Adriana-28/Repositorio_grupo_13/Imágenes/1.png

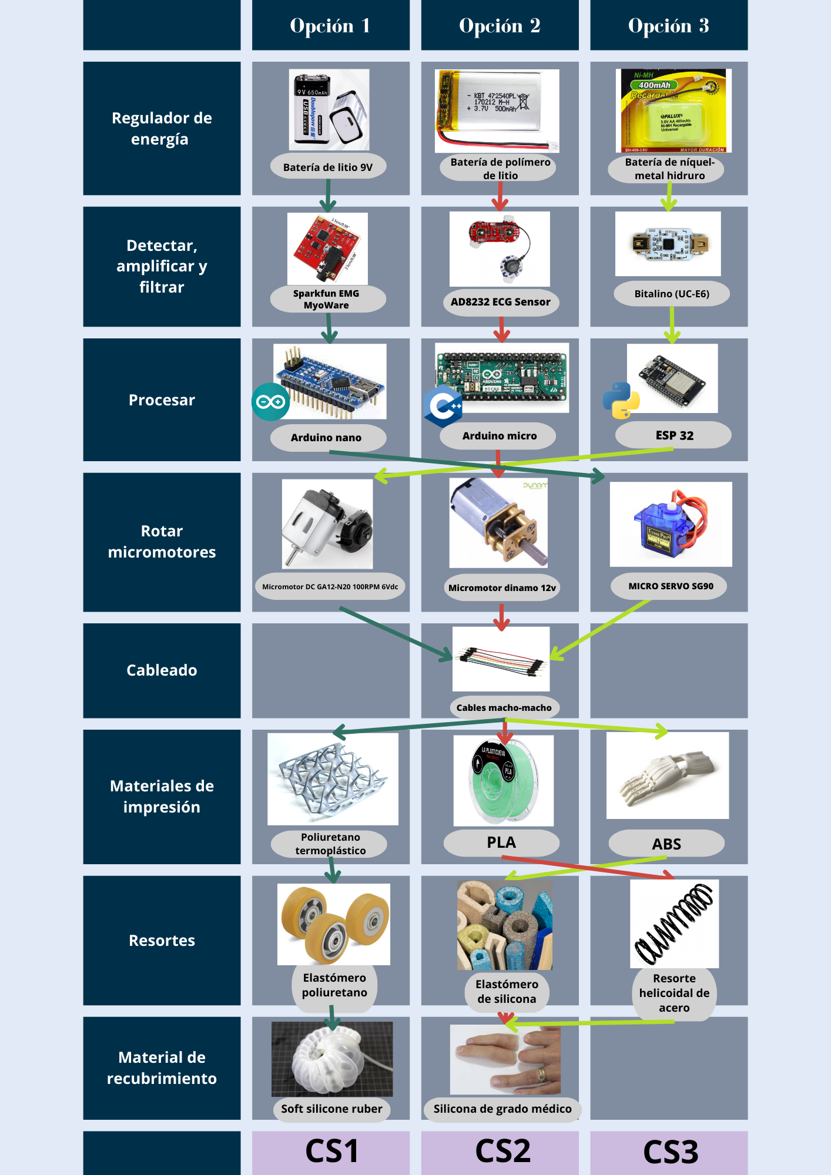
Imágenes/1.png
