Adriana-28/Repositorio_grupo_13/Imágenes/2.png

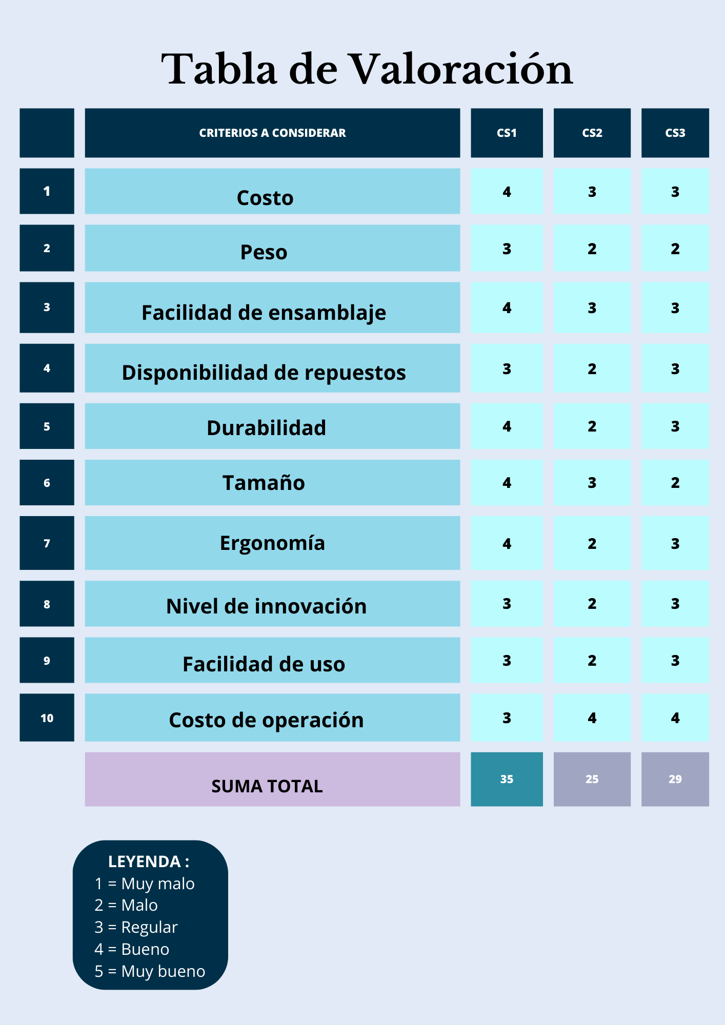
Imágenes/2.png
