Adriana-28/Repositorio_grupo_13/Imágenes/Captura de pantalla 2023-09-21 232807.png

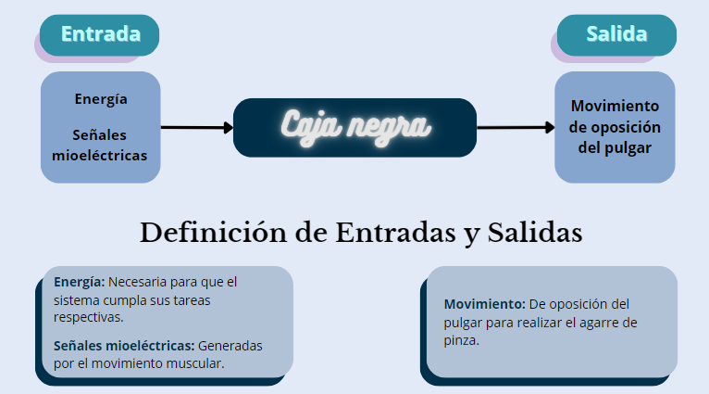
Imágenes/Captura de pantalla 2023-09-21 232807.png
