Adriana-28/Repositorio_grupo_13/Imágenes/Captura de pantalla 2023-09-21 233254.png

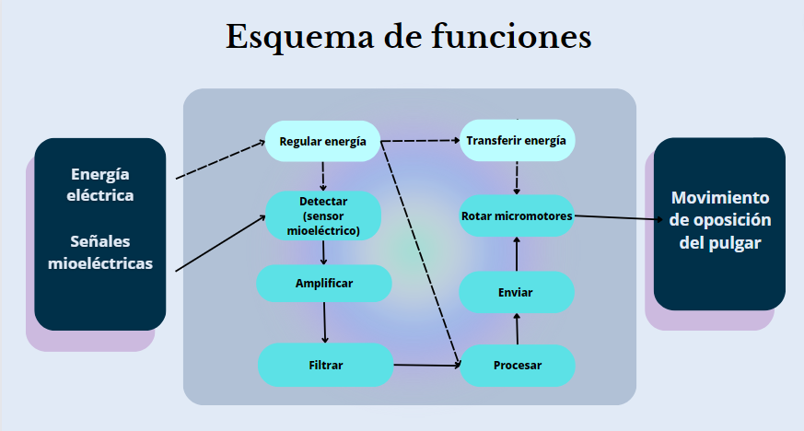
Imágenes/Captura de pantalla 2023-09-21 233254.png
