Adriana-28/Repositorio_grupo_13/Imágenes/Captura de pantalla 2023-10-20 073522.png

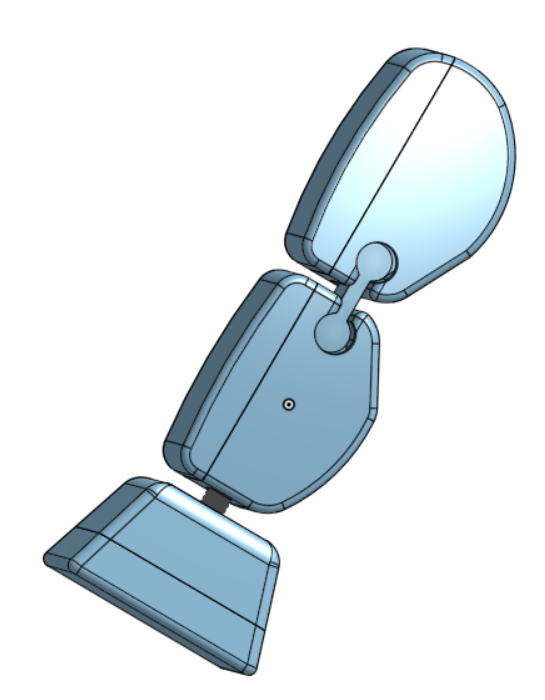
Imágenes/Captura de pantalla 2023-10-20 073522.png
