Adriana-28/Repositorio_grupo_13/Imágenes/Captura de pantalla 2023-11-03 025052.png

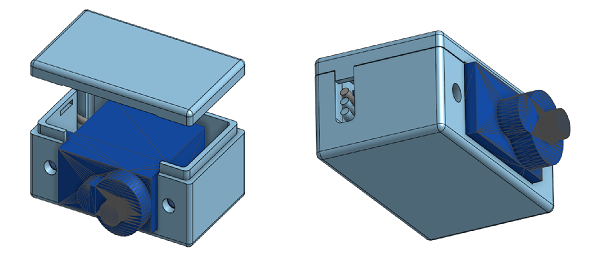
Imágenes/Captura de pantalla 2023-11-03 025052.png
