Adriana-28/Repositorio_grupo_13/Imágenes/Captura de pantalla 2023-11-24 012323.png

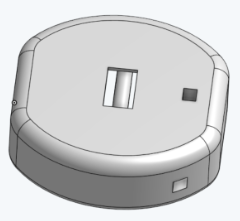
Imágenes/Captura de pantalla 2023-11-24 012323.png
