Adriana-28/Repositorio_grupo_13/Imágenes/Captura de pantalla 2023-11-24 012328.png

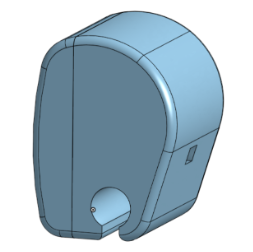
Imágenes/Captura de pantalla 2023-11-24 012328.png
