Adriana-28/Repositorio_grupo_13/Imágenes/Esquema de funciones.png

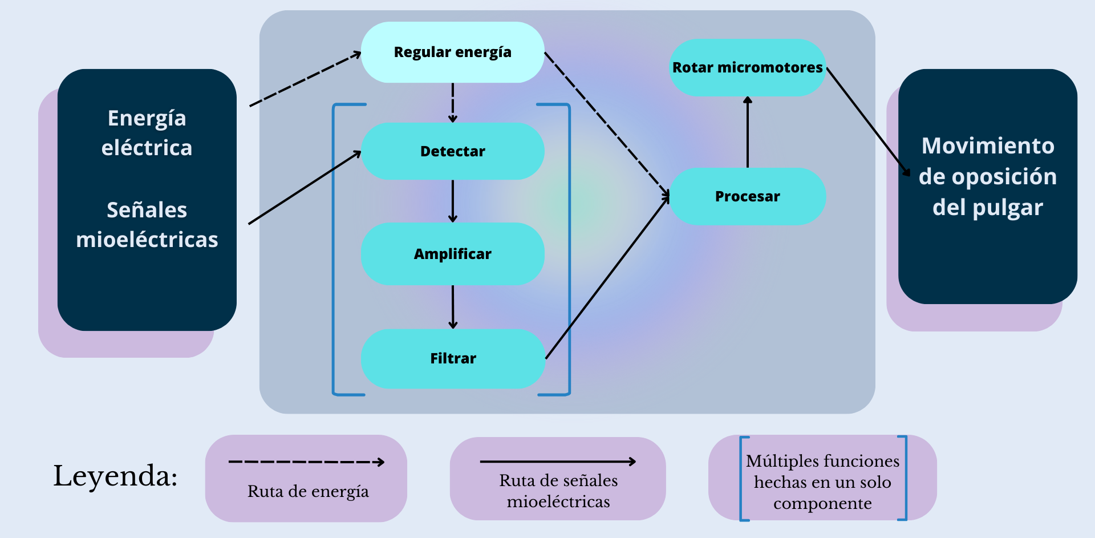
Imágenes/Esquema de funciones.png
