Adriana-28/Repositorio_grupo_13/Imágenes/Foto Alessia.jpeg

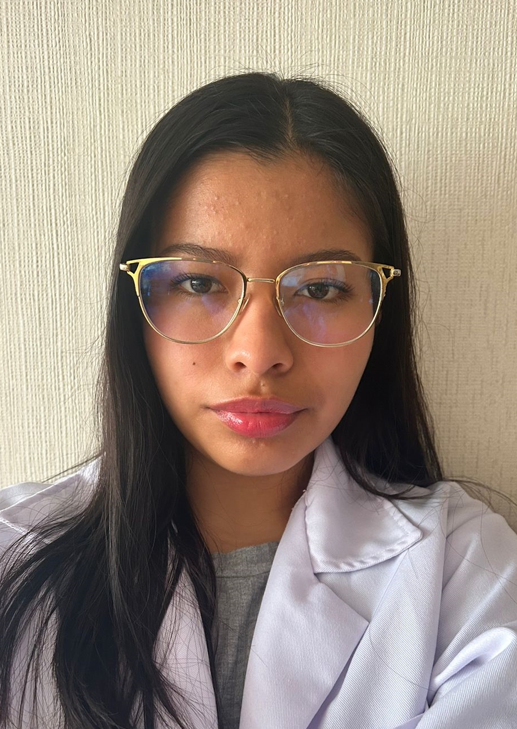
Imágenes/Foto Alessia.jpeg
