Adriana-28/Repositorio_grupo_13/Imágenes/Matriz morfológica (1).png

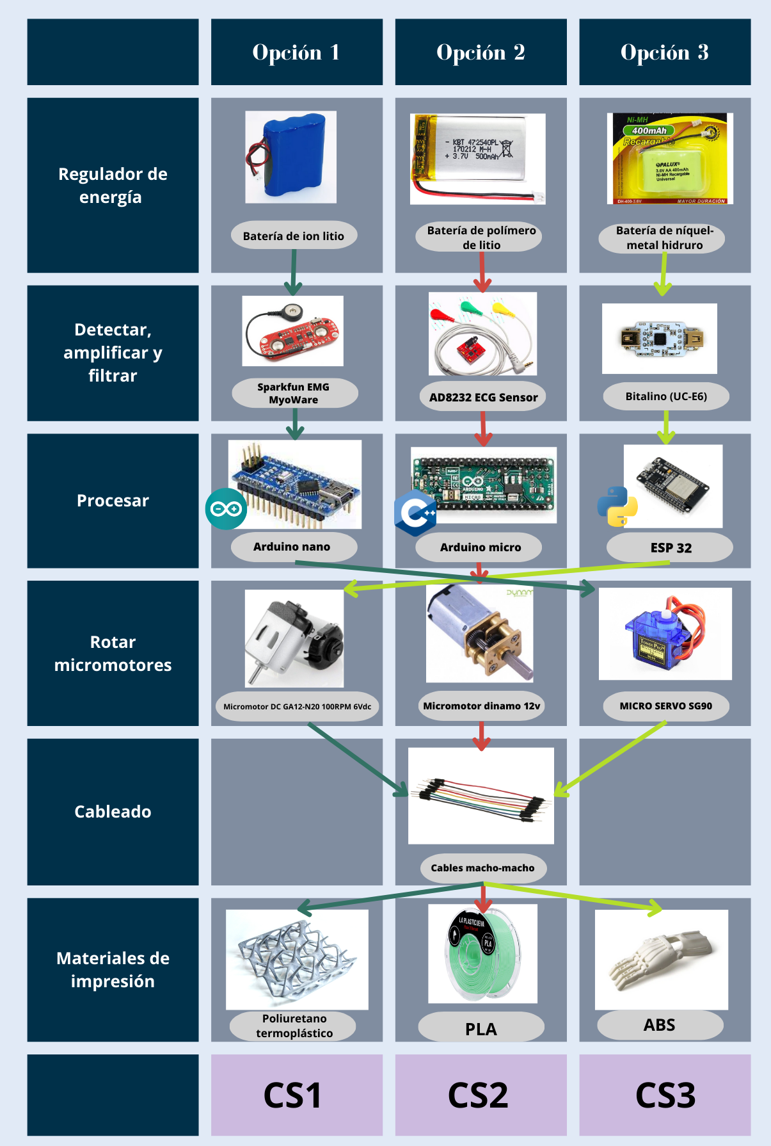
Imágenes/Matriz morfológica (1).png
