Adriana-28/Repositorio_grupo_13/Imágenes/Patente mano.jpeg

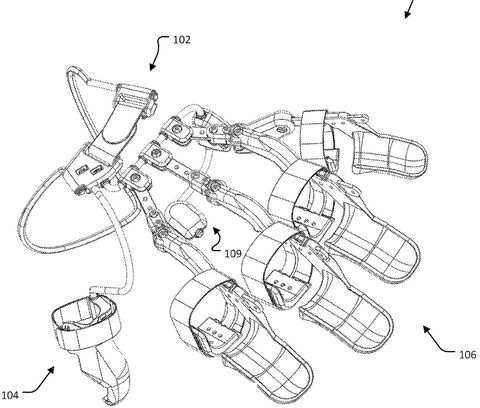
Imágenes/Patente mano.jpeg
