Adriana-28/Repositorio_grupo_13/Imágenes/Patente pulgar.jpeg

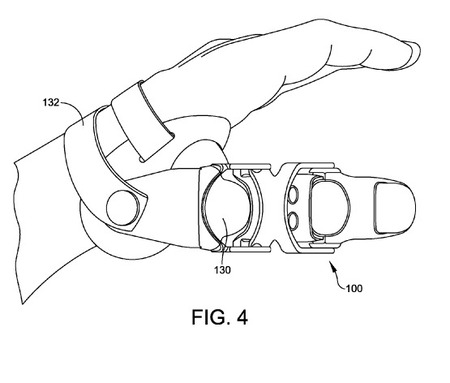
Imágenes/Patente pulgar.jpeg
