Adriana-28/Repositorio_grupo_13/Imágenes/Tabla de valoración.png

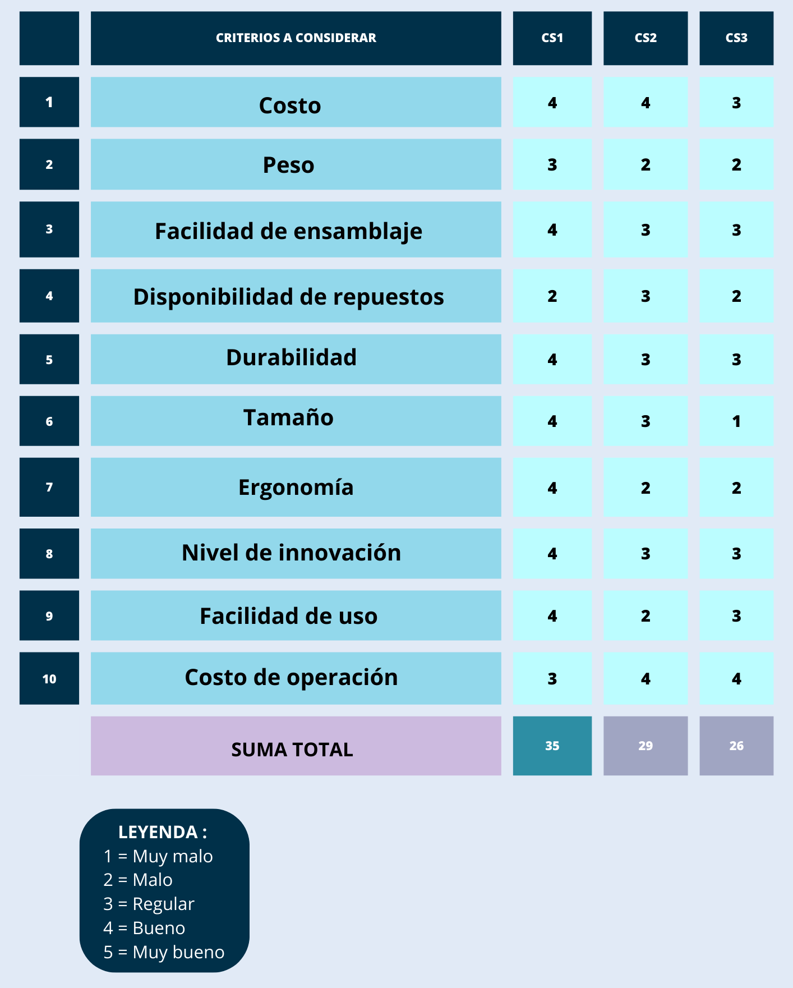
Imágenes/Tabla de valoración.png
