Adriana-28/Repositorio_grupo_13/Imágenes/WhatsApp Image 2023-09-21 at 20.53.01.jpeg

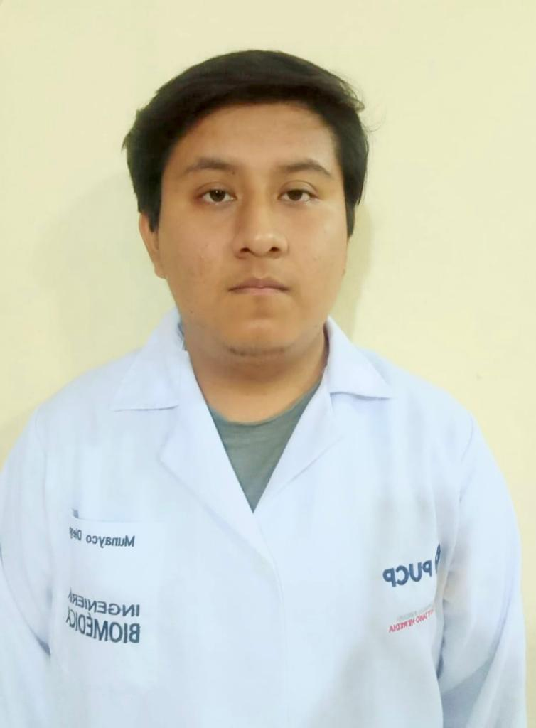
Imágenes/WhatsApp Image 2023-09-21 at 20.53.01.jpeg
