Adriana-28/Repositorio_grupo_13/Imágenes/WhatsApp Image 2023-09-21 at 22.54.08.jpeg

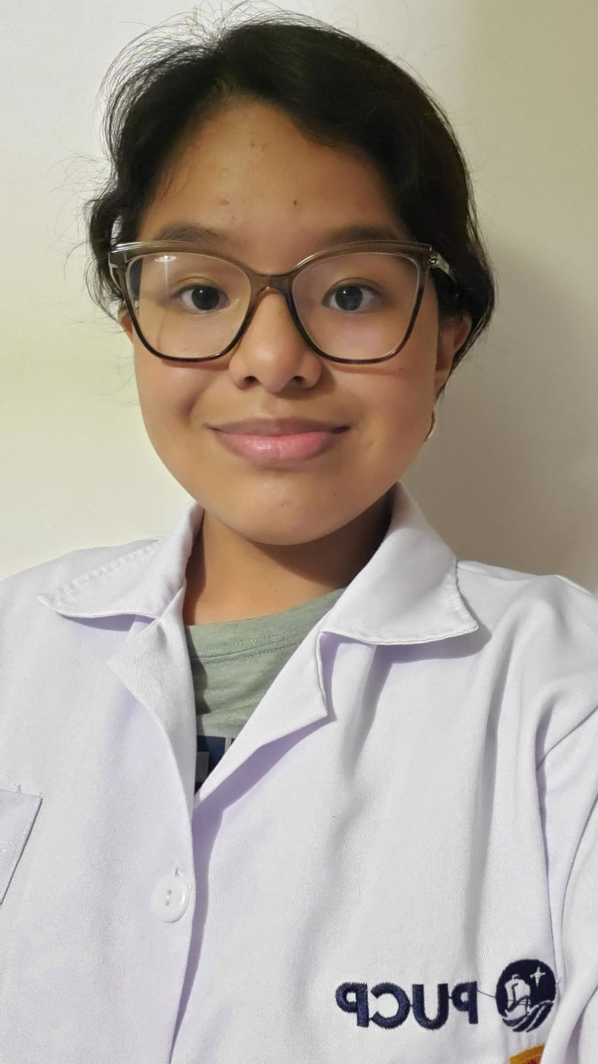
Imágenes/WhatsApp Image 2023-09-21 at 22.54.08.jpeg
