Adriana-28/Repositorio_grupo_13/Imágenes/WhatsApp Image 2023-09-28 at 23.58.50.jpeg

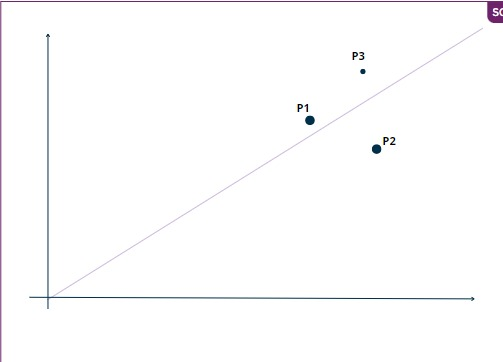
Imágenes/WhatsApp Image 2023-09-28 at 23.58.50.jpeg
