Adriana-28/Repositorio_grupo_13/Imágenes/WhatsApp Image 2023-11-03 at 02.50.23.jpeg

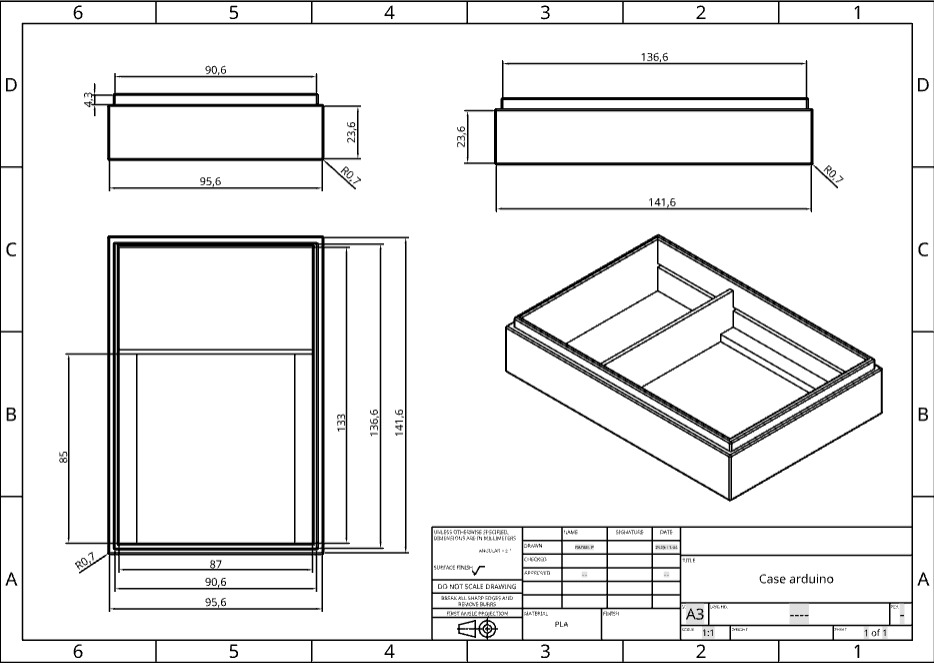
Imágenes/WhatsApp Image 2023-11-03 at 02.50.23.jpeg
