Adriana-28/Repositorio_grupo_13/Modelado/Planos de las piezas/Base_1.pdf

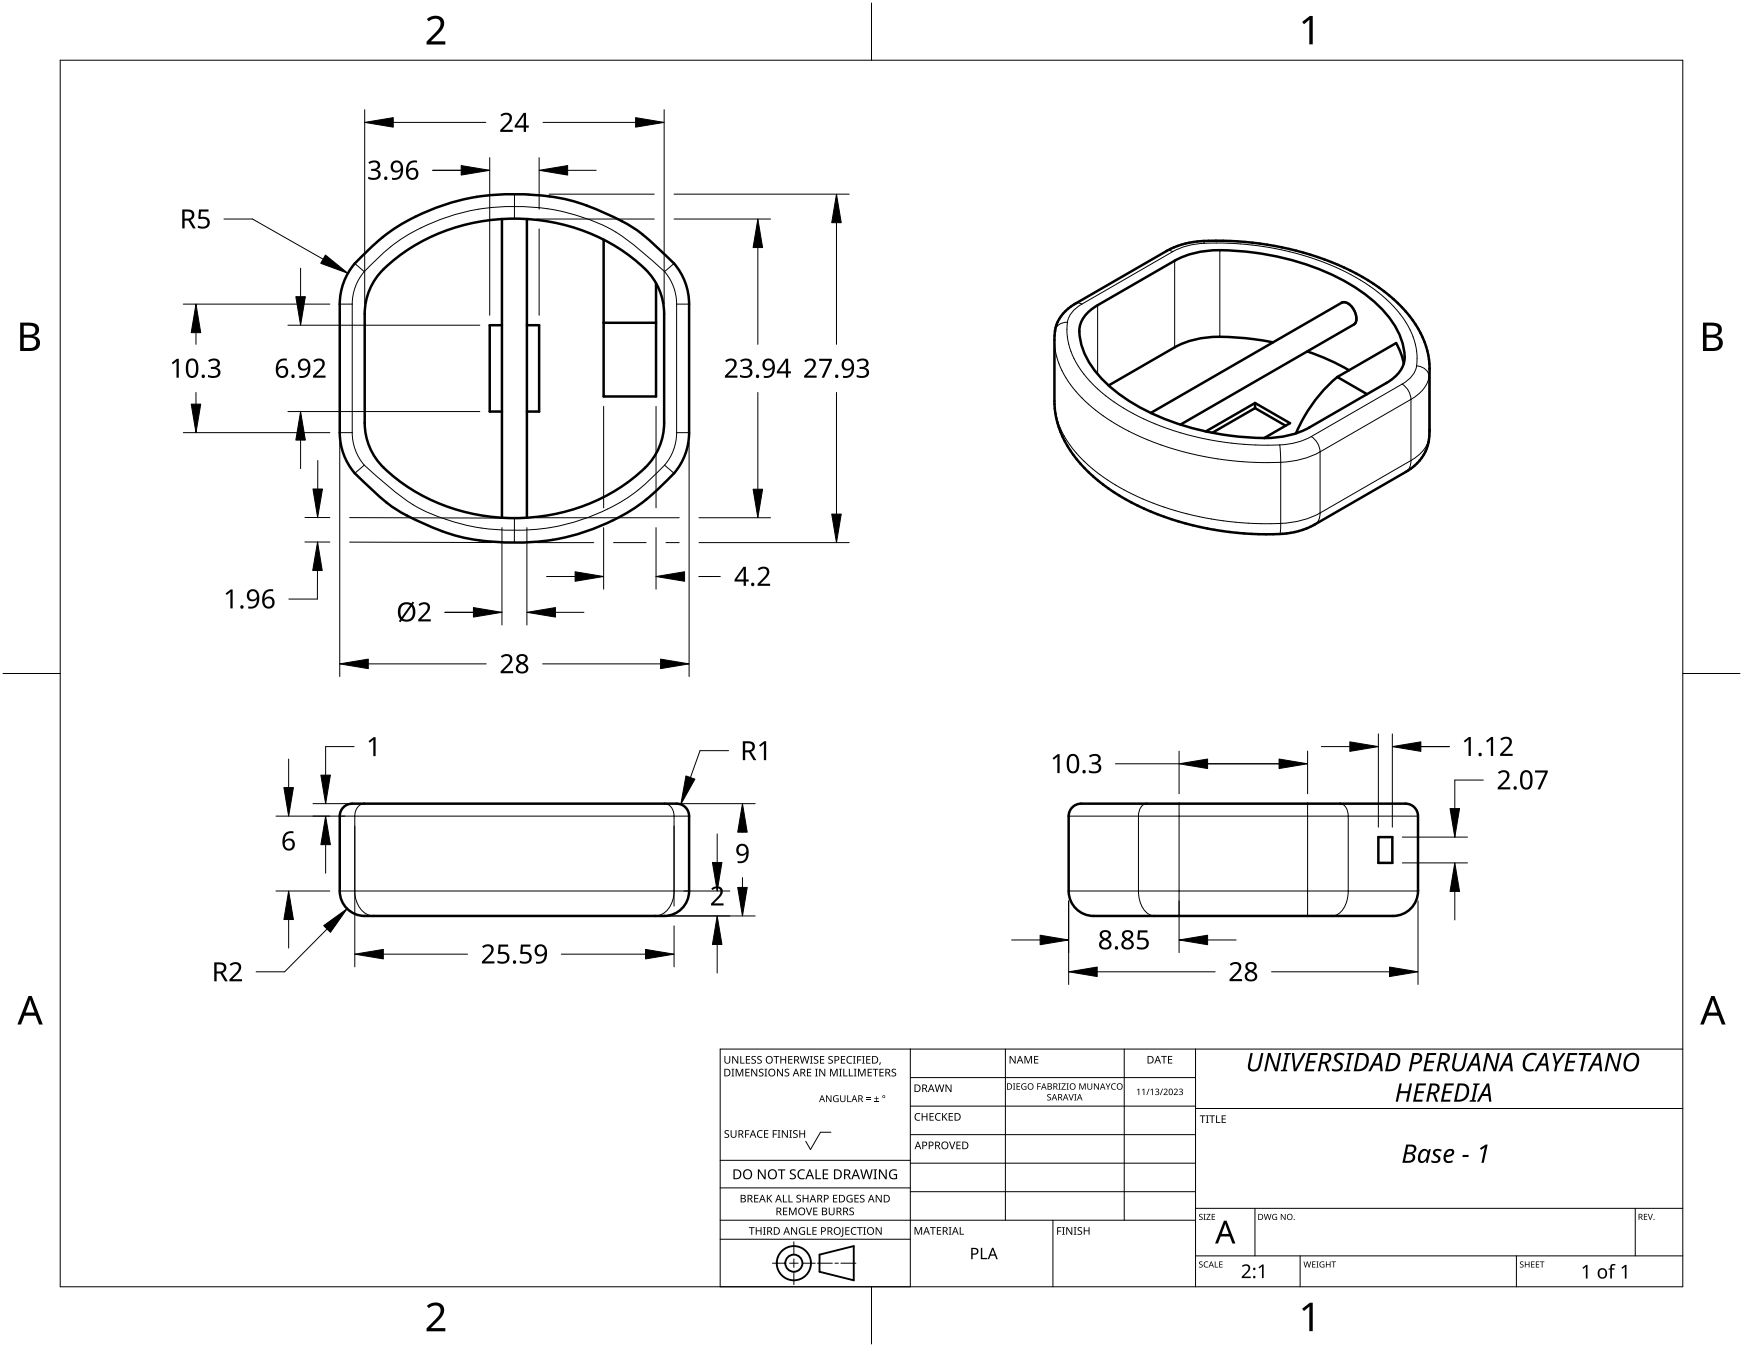
[picture p146: page 1]
