Adriana-28/Repositorio_grupo_13/Modelado/Planos de las piezas/Base_2.pdf

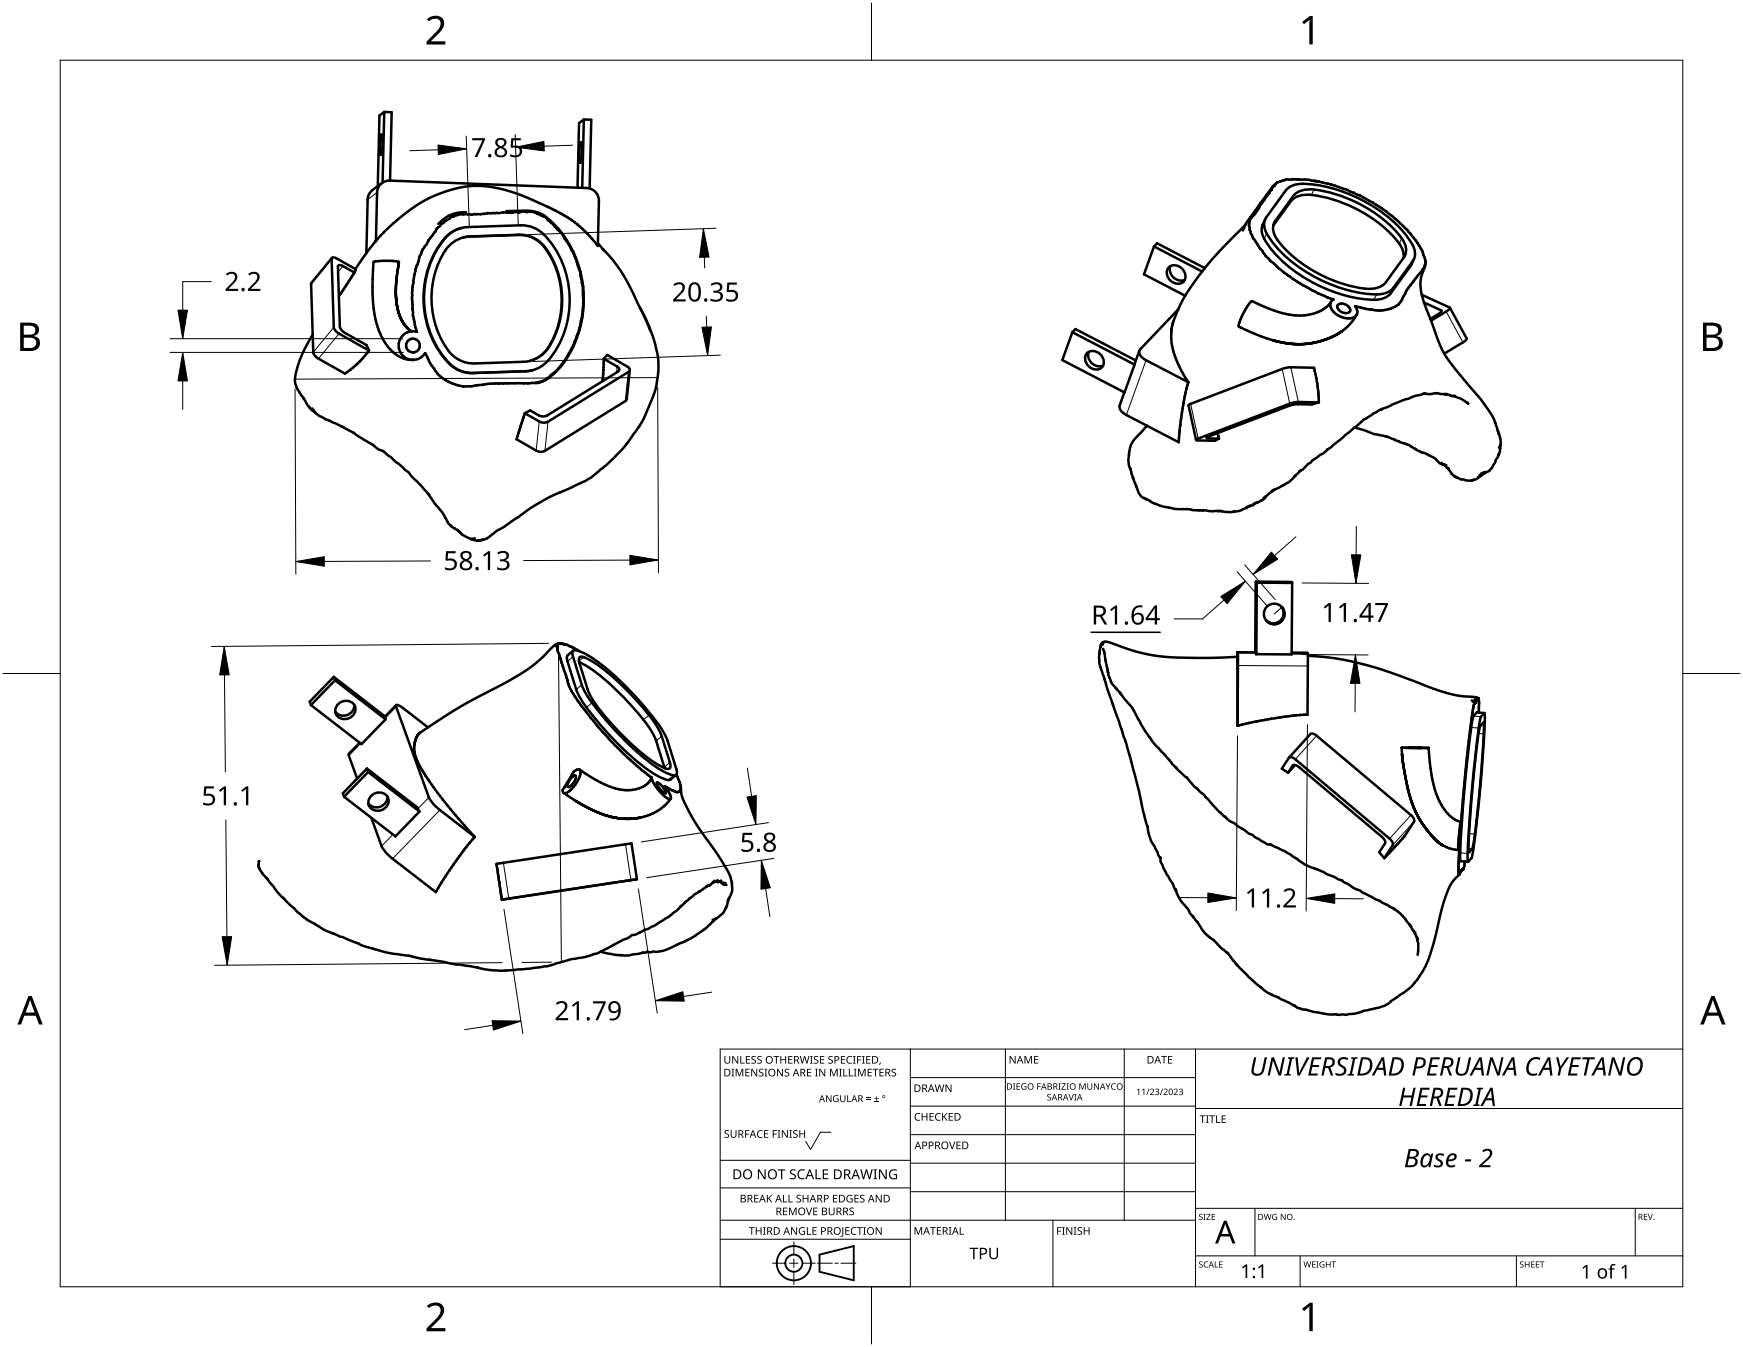
[picture p147: page 1]
