Adriana-28/Repositorio_grupo_13/Modelado/Planos de las piezas/Elastómero.pdf

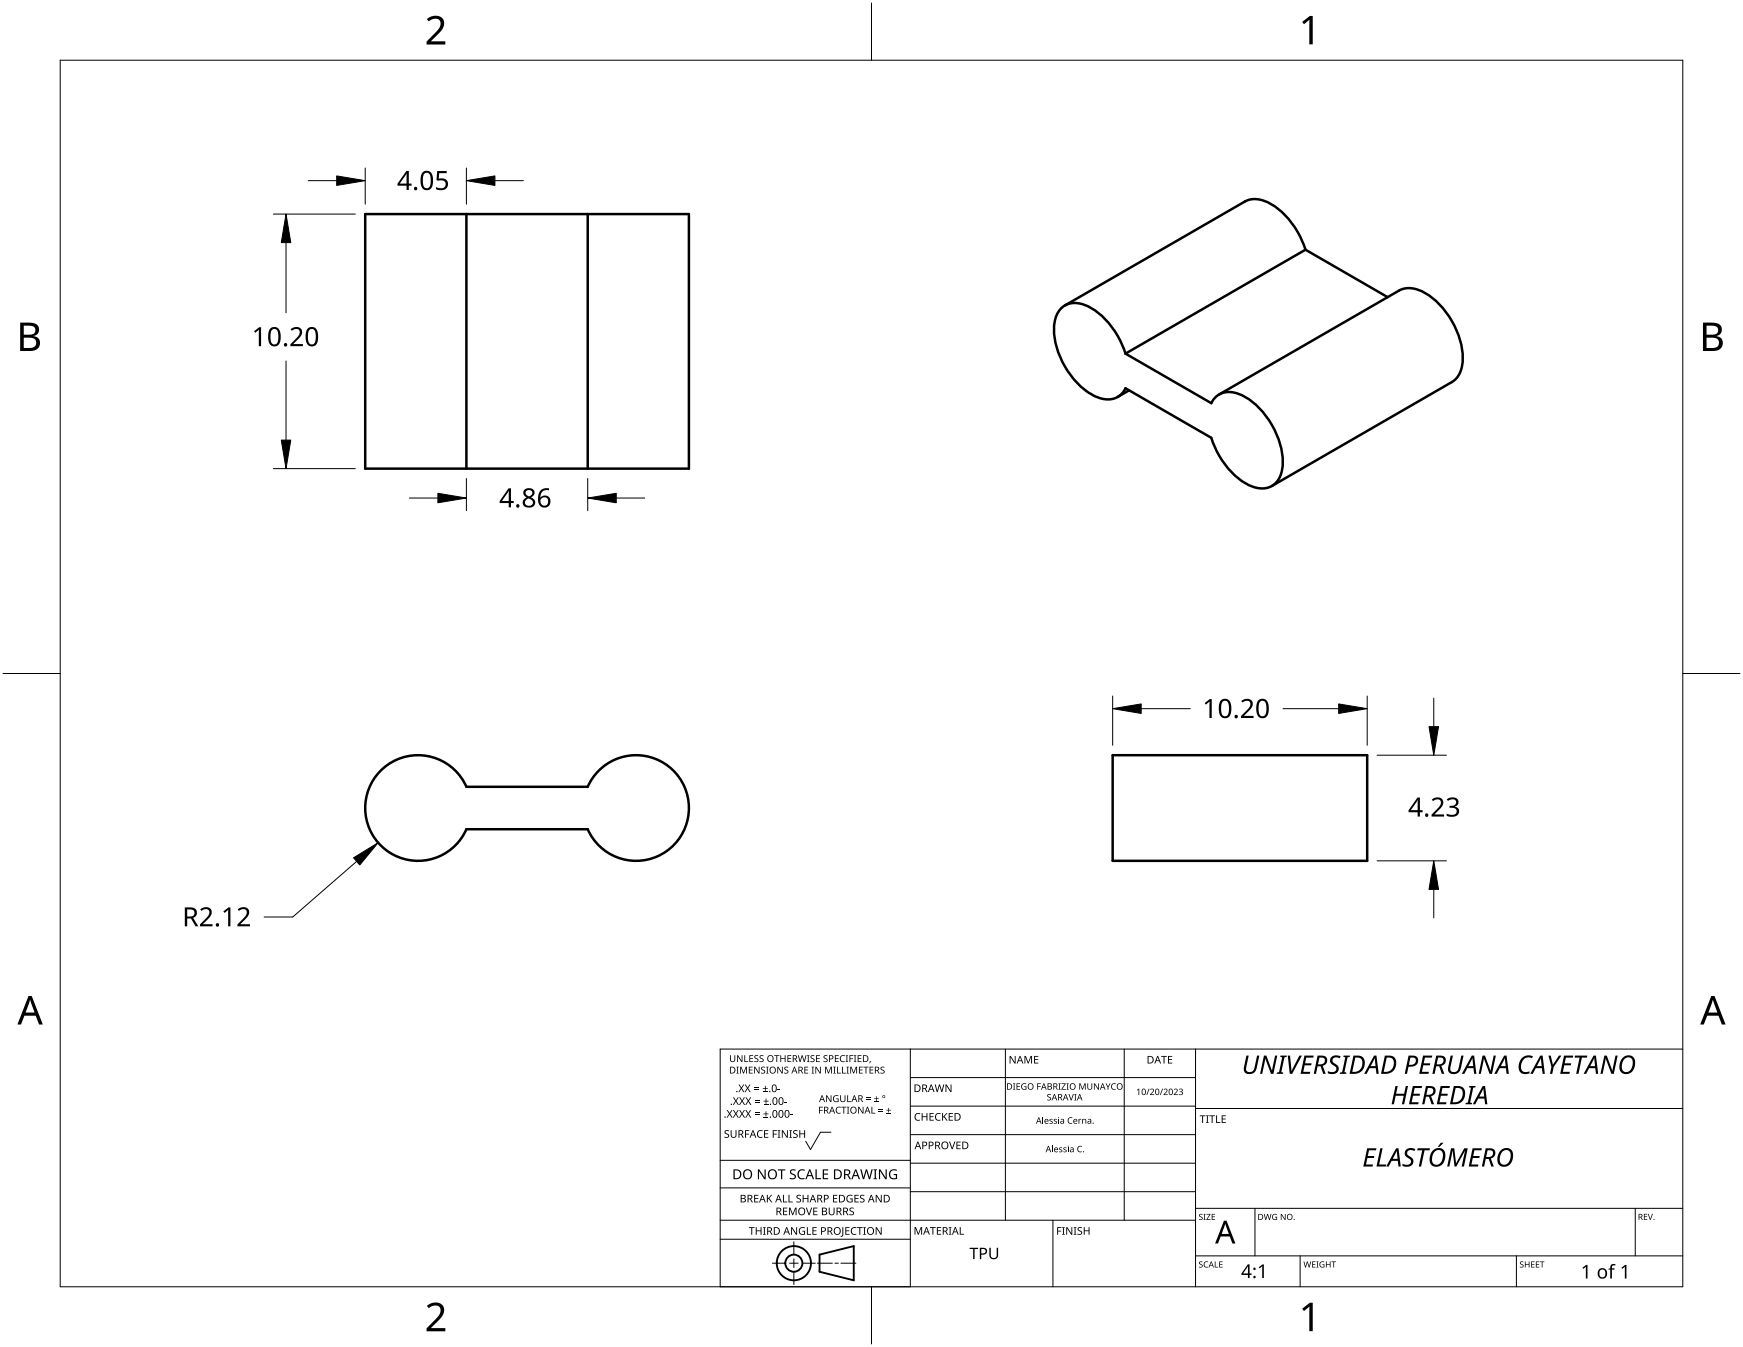
[picture p148: page 1]
