Adriana-28/Repositorio_grupo_13/Modelado/Planos de las piezas/Falange D_1.pdf

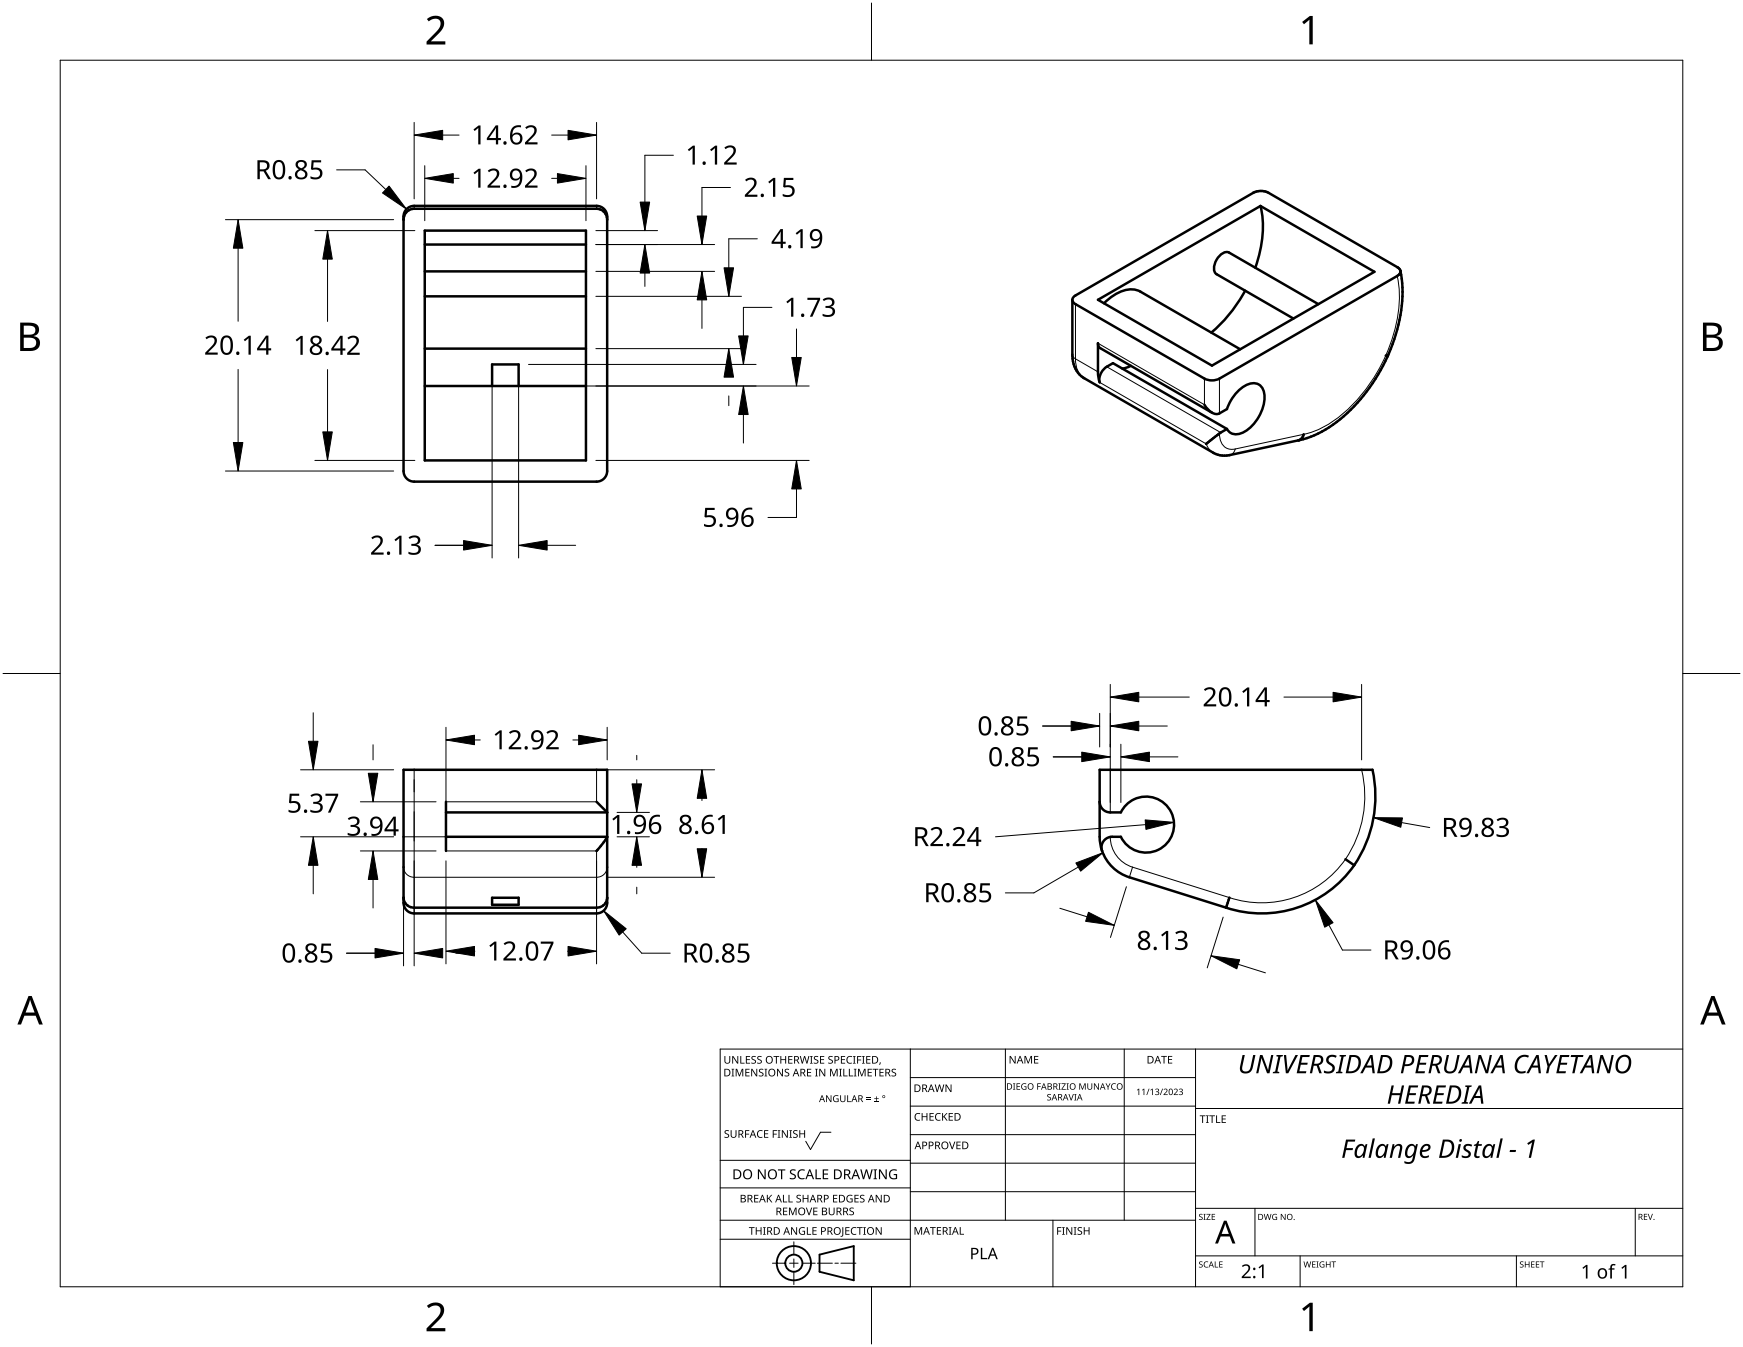
[picture p149: page 1]
