Adriana-28/Repositorio_grupo_13/Modelado/Planos de las piezas/Falange D_2.pdf

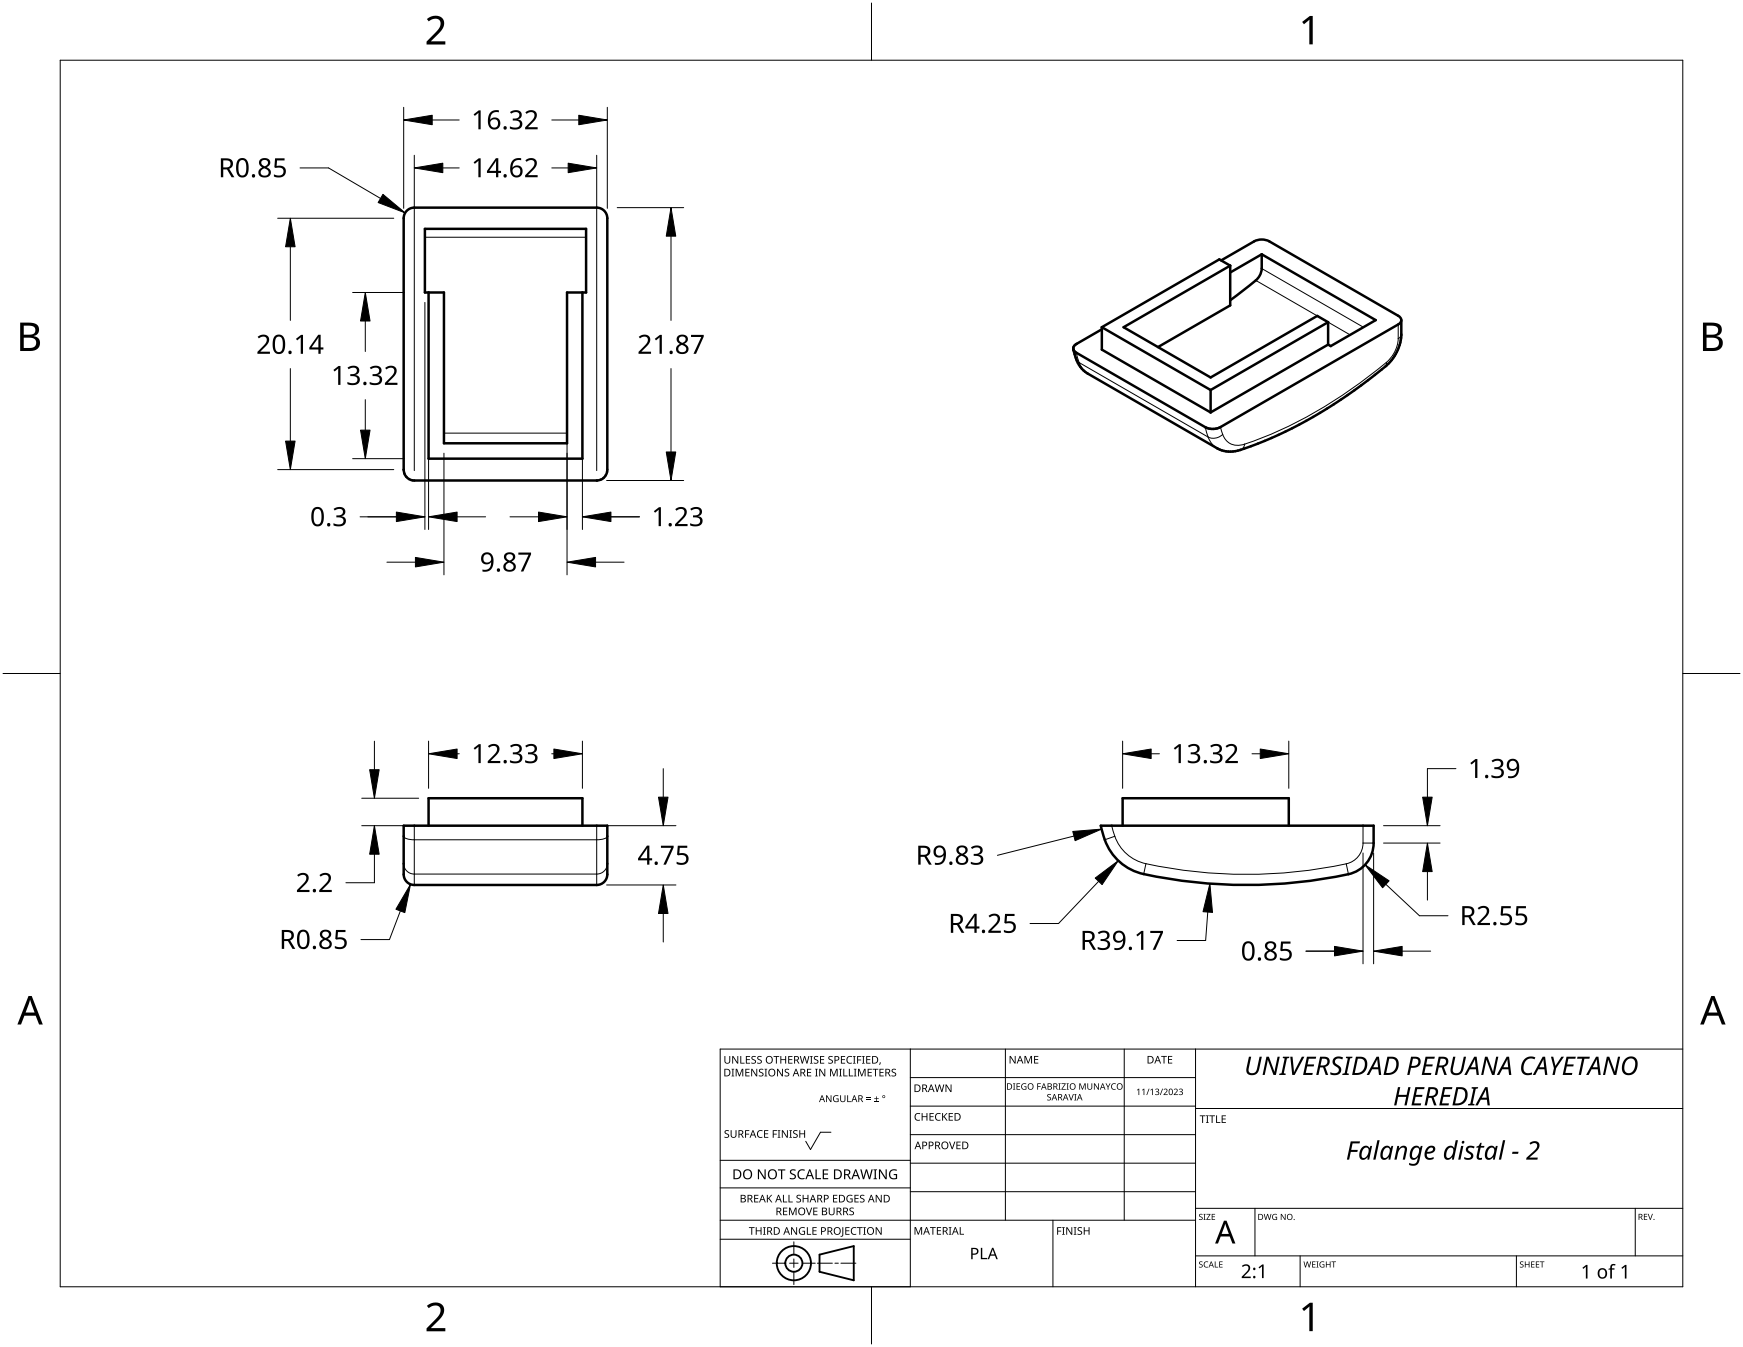
[picture p150: page 1]
