Adriana-28/Repositorio_grupo_13/Modelado/Planos de las piezas/Falange P_1.pdf

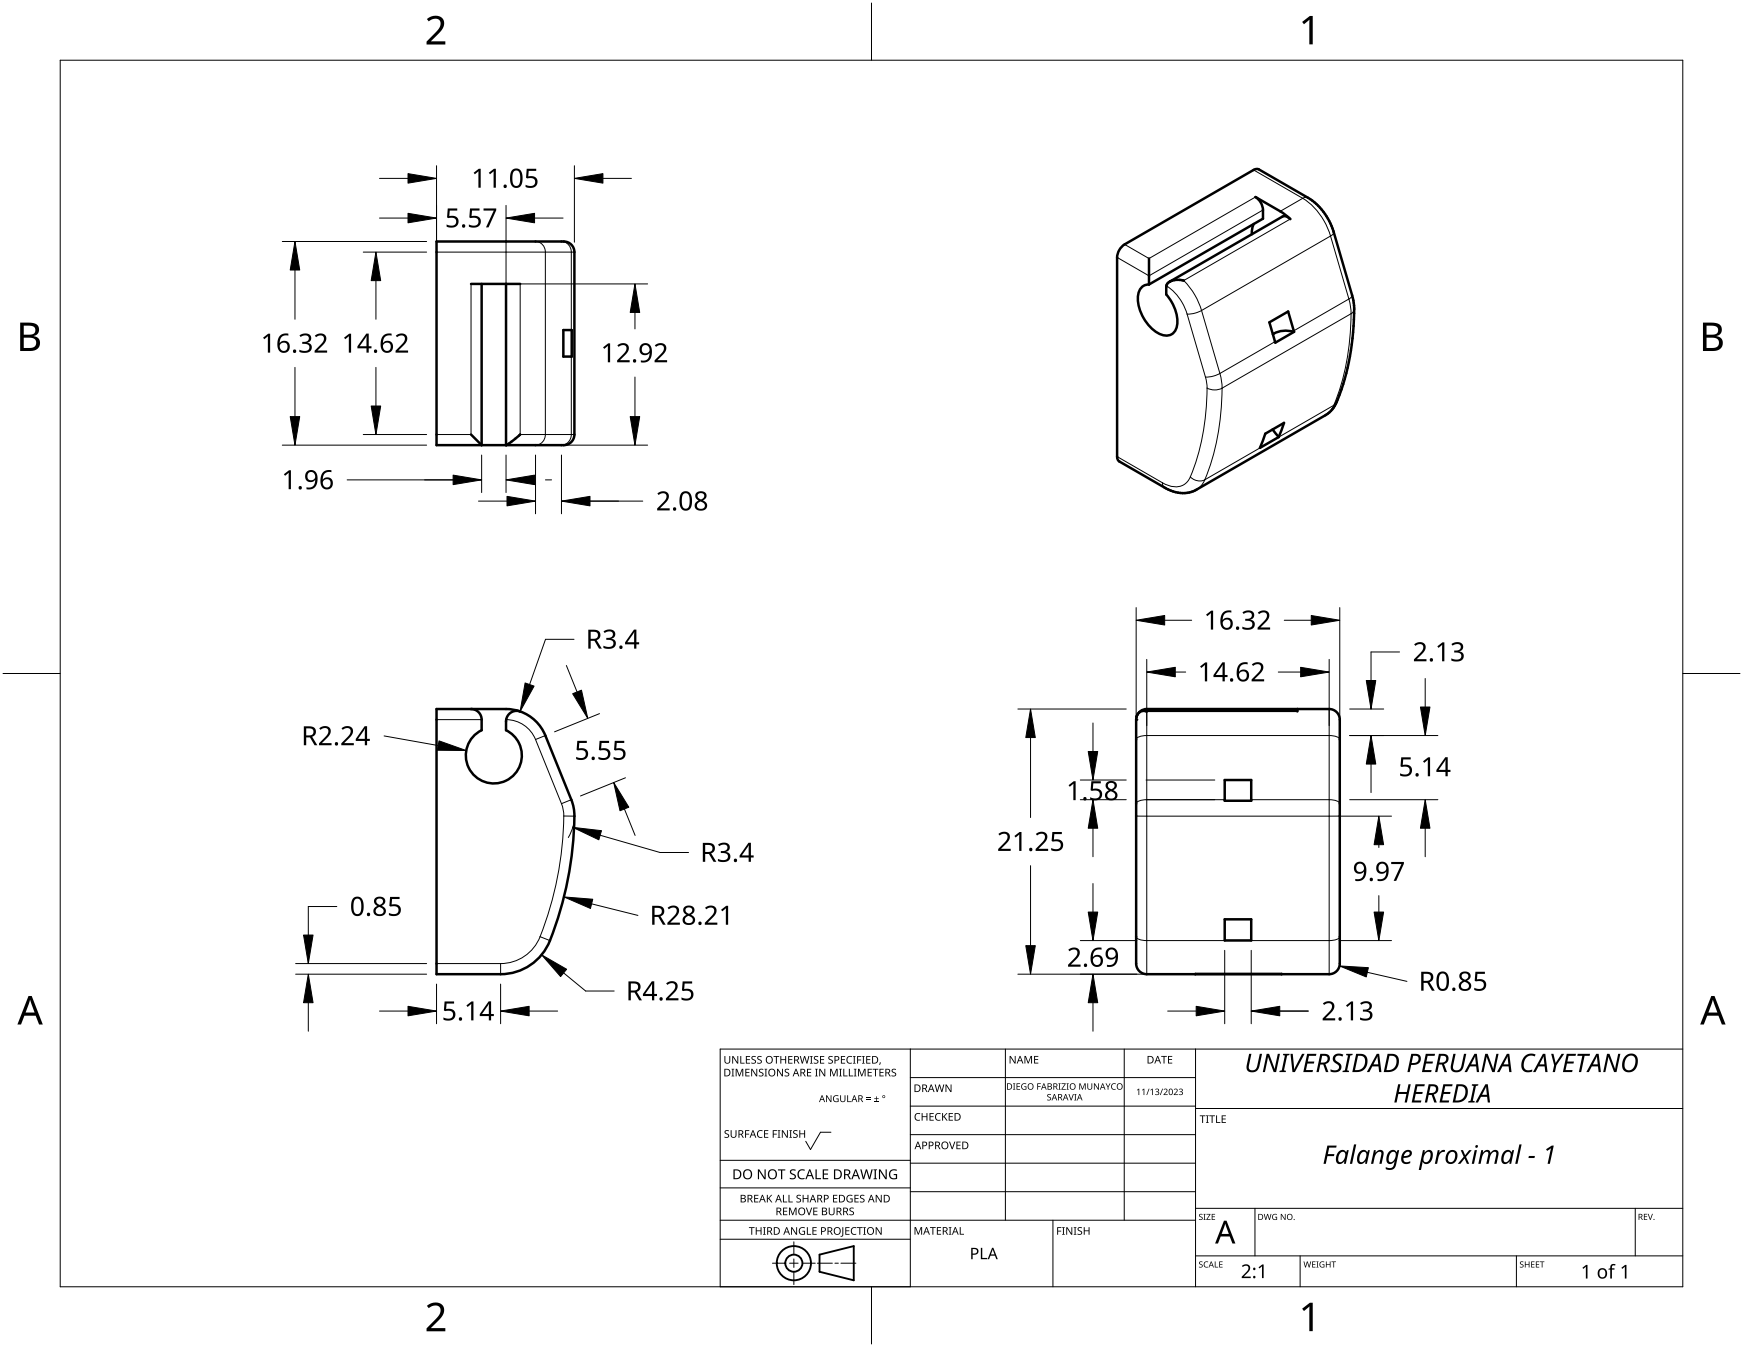
[picture p151: page 1]
