Adriana-28/Repositorio_grupo_13/Modelado/Planos de las piezas/Falange P_2.pdf

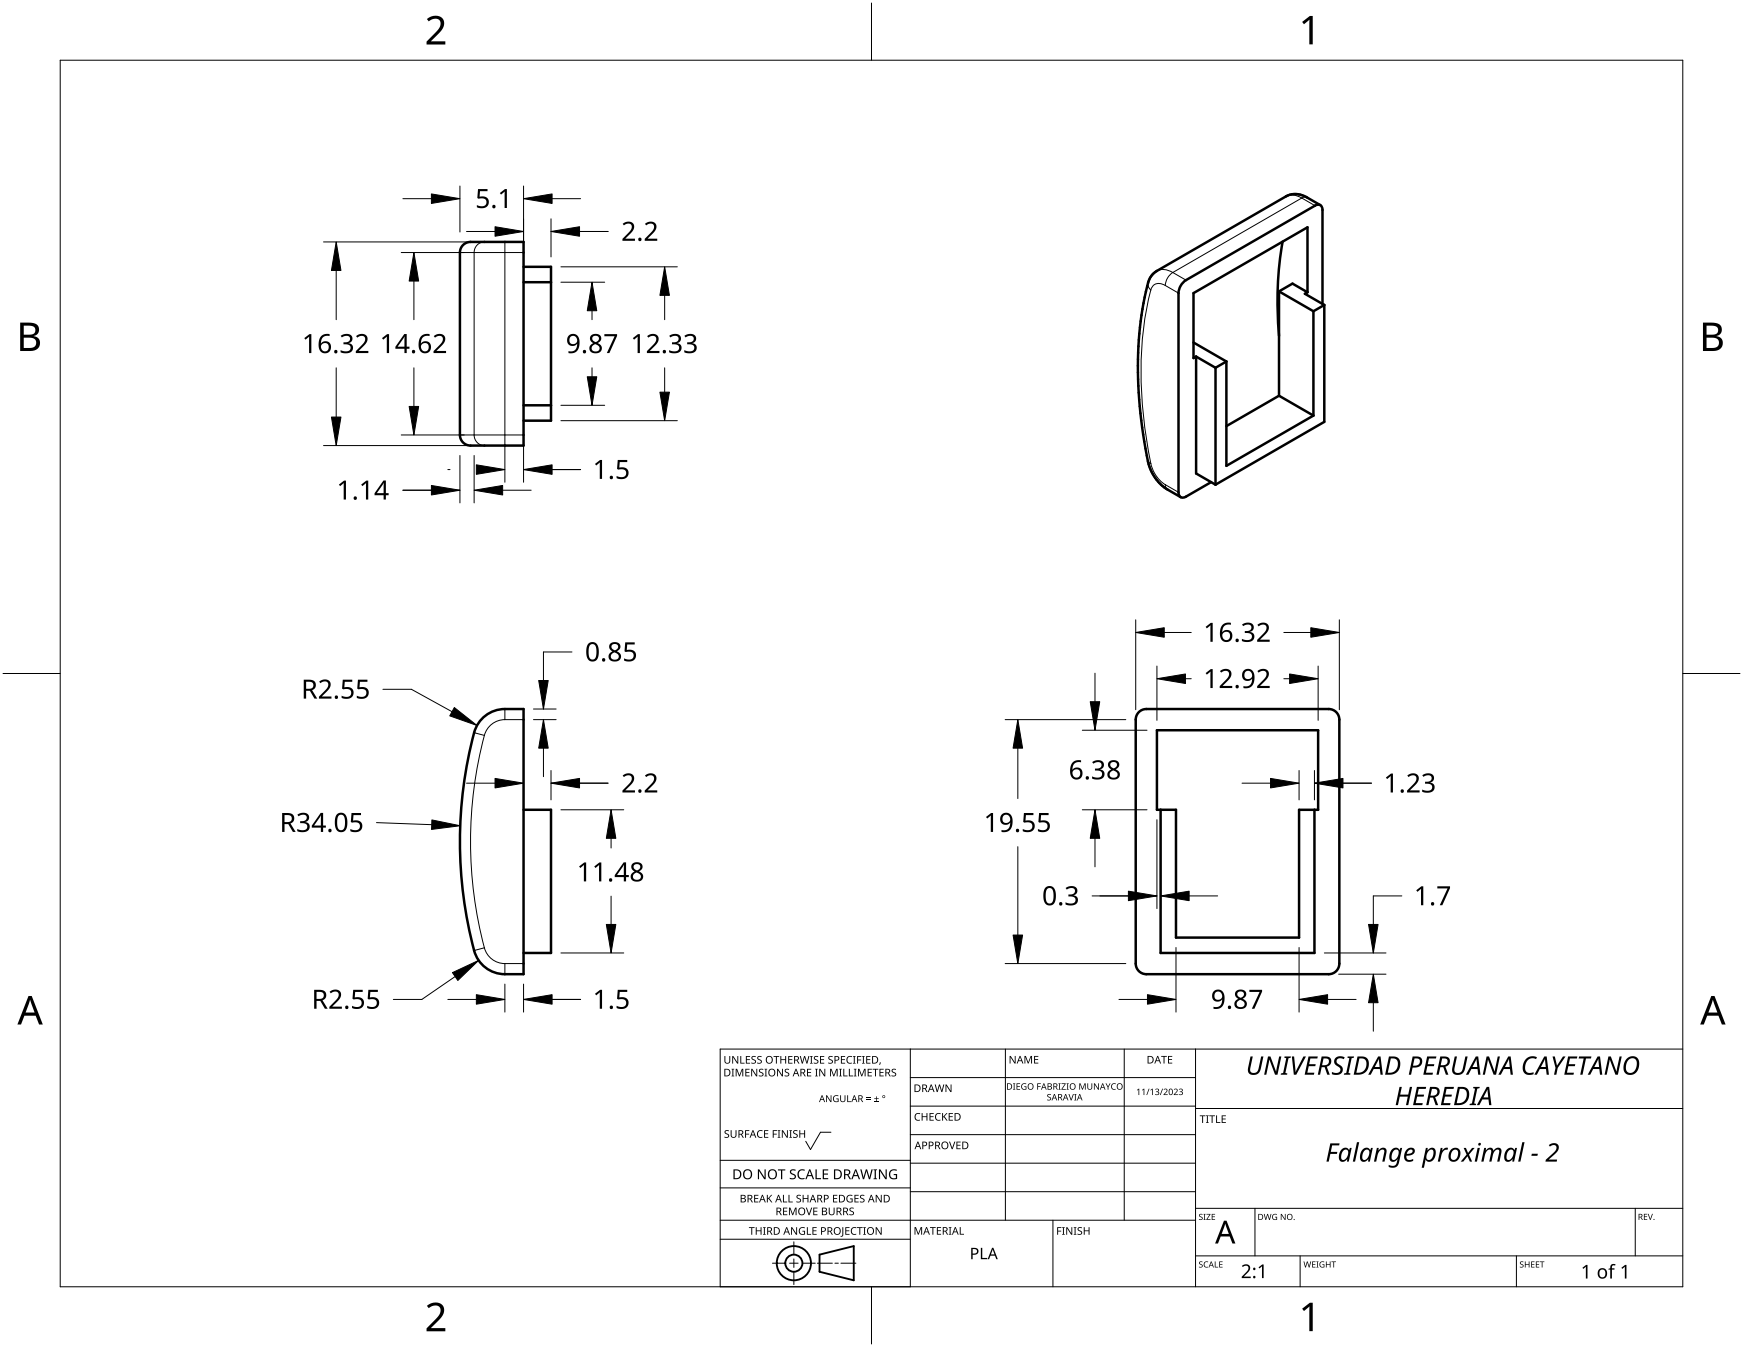
[picture p152: page 1]
