Adriana-28/Repositorio_grupo_13/Modelado/Planos de las piezas/Plano Case Sensor EMG.pdf

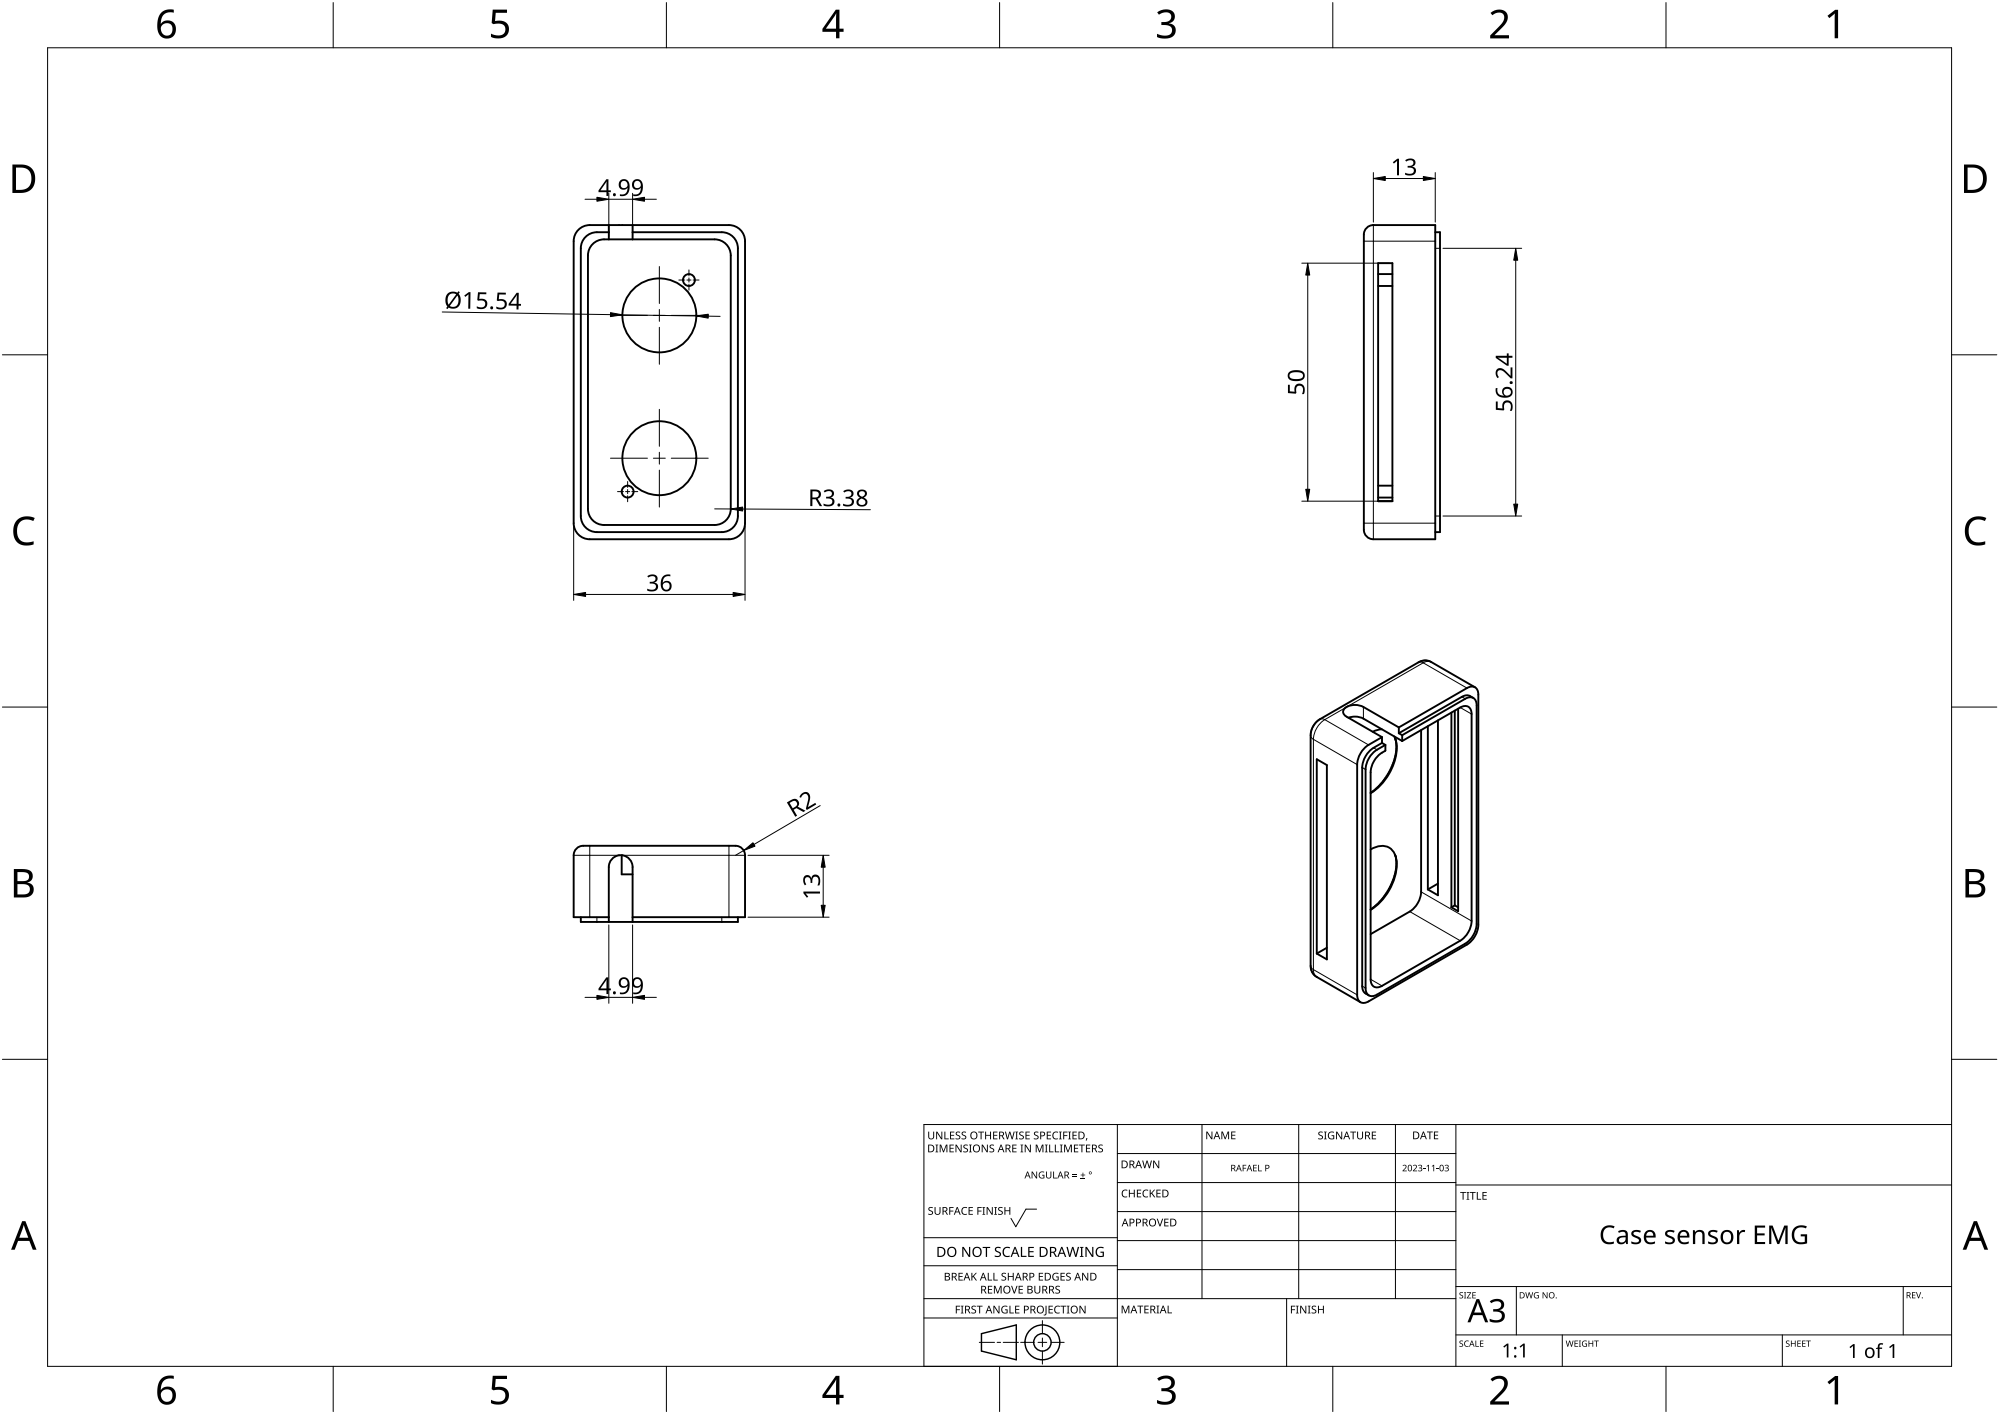
[picture p153: page 1]
