Adriana-28/Repositorio_grupo_13/Modelado/Planos de las piezas/Plano Case Servomotor.pdf

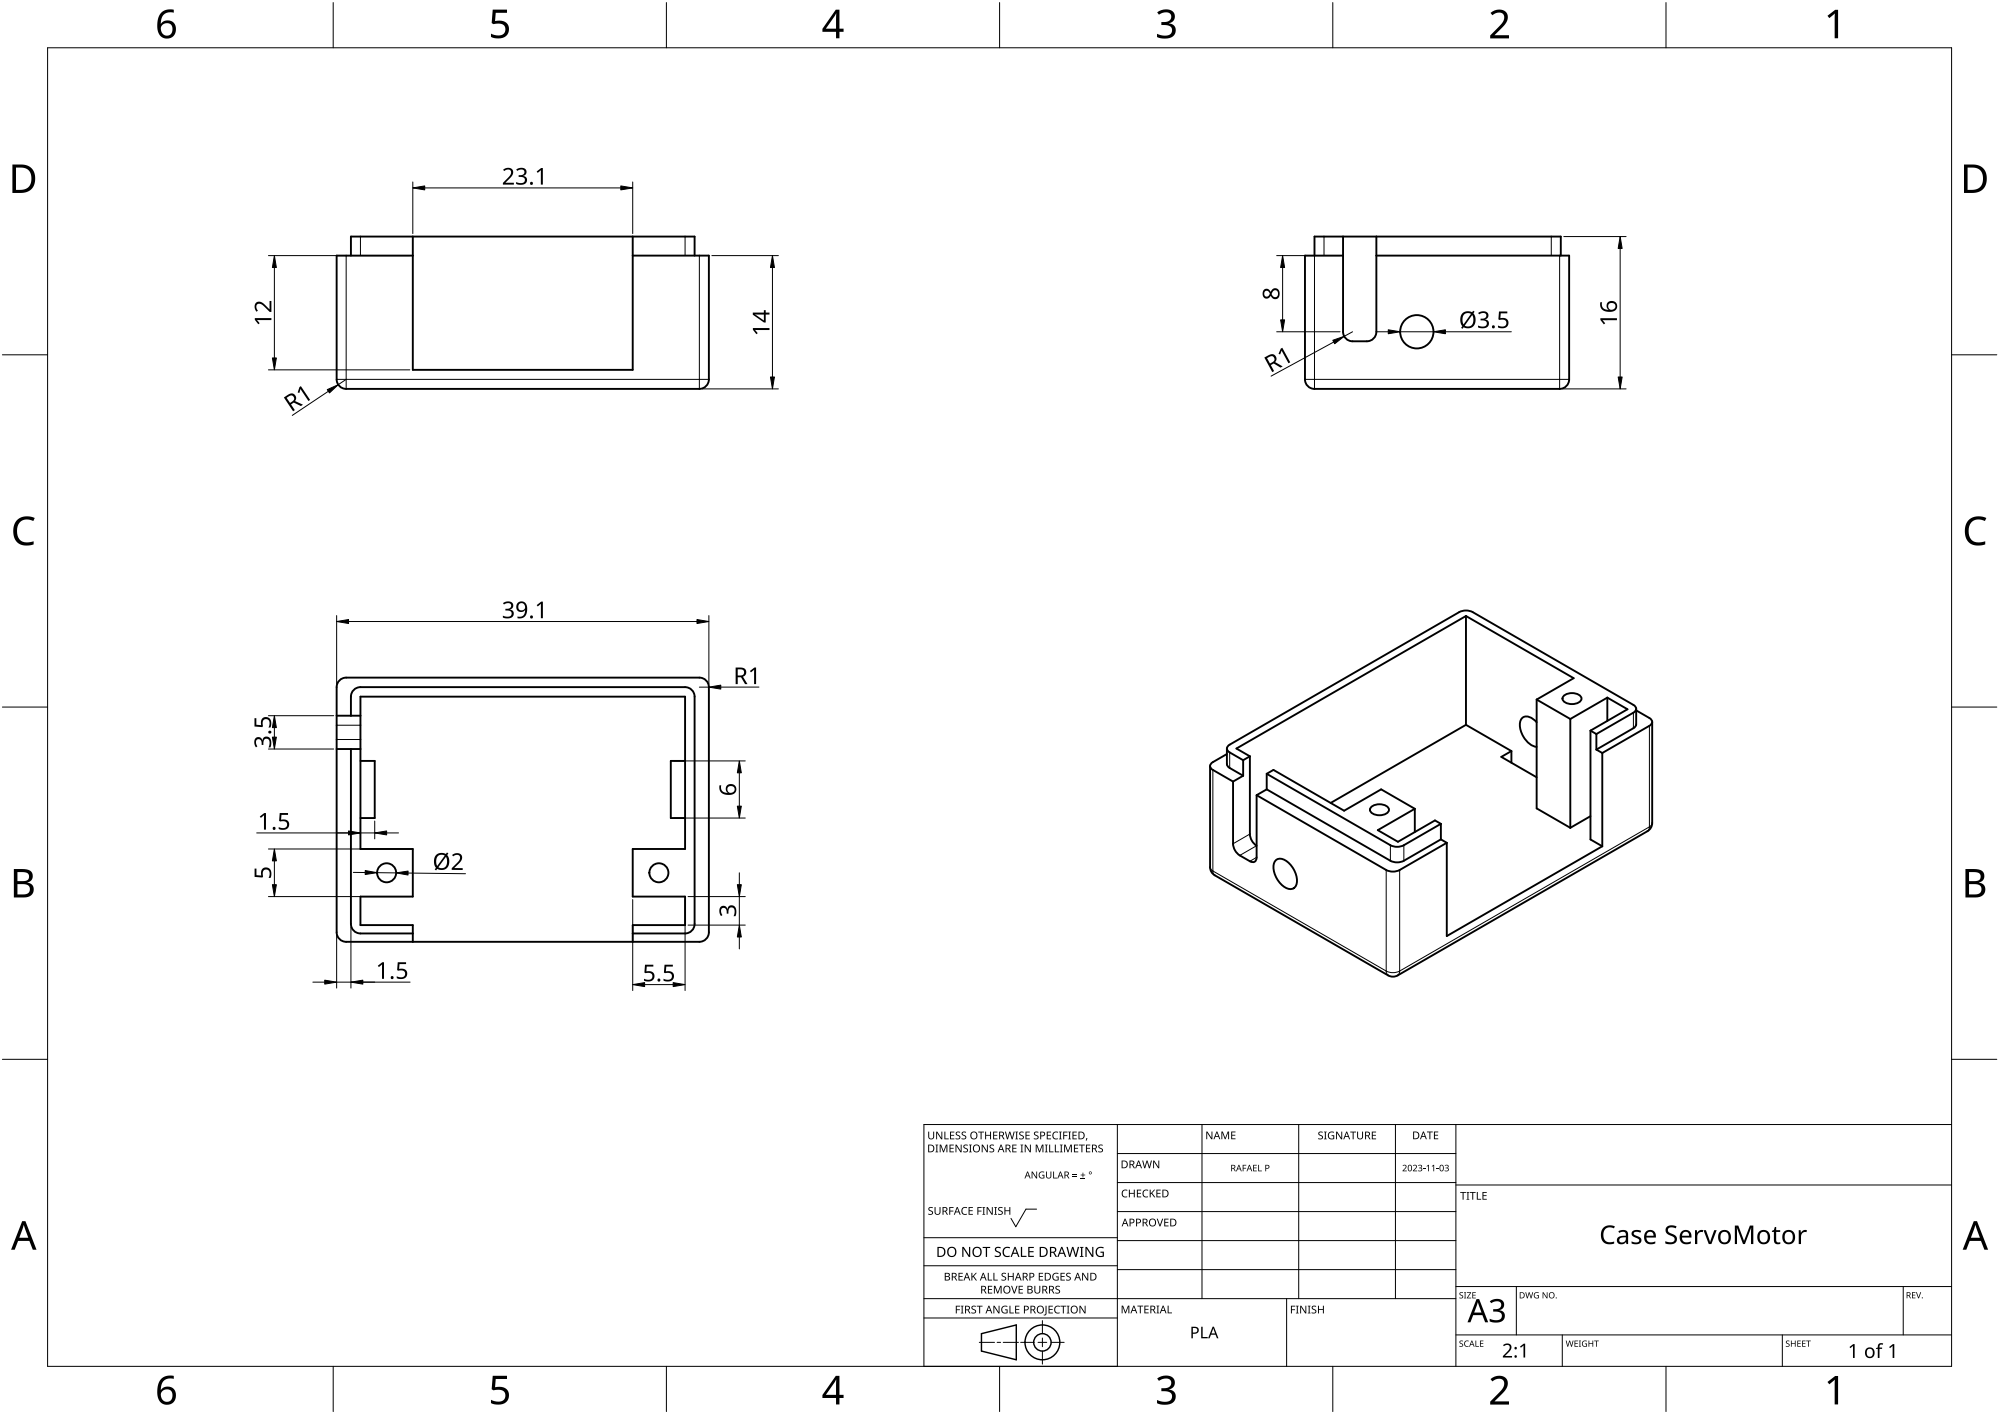
[picture p154: page 1]
