Adriana-28/Repositorio_grupo_13/Modelado/Planos de las piezas/Plano de la tapa del servo.pdf

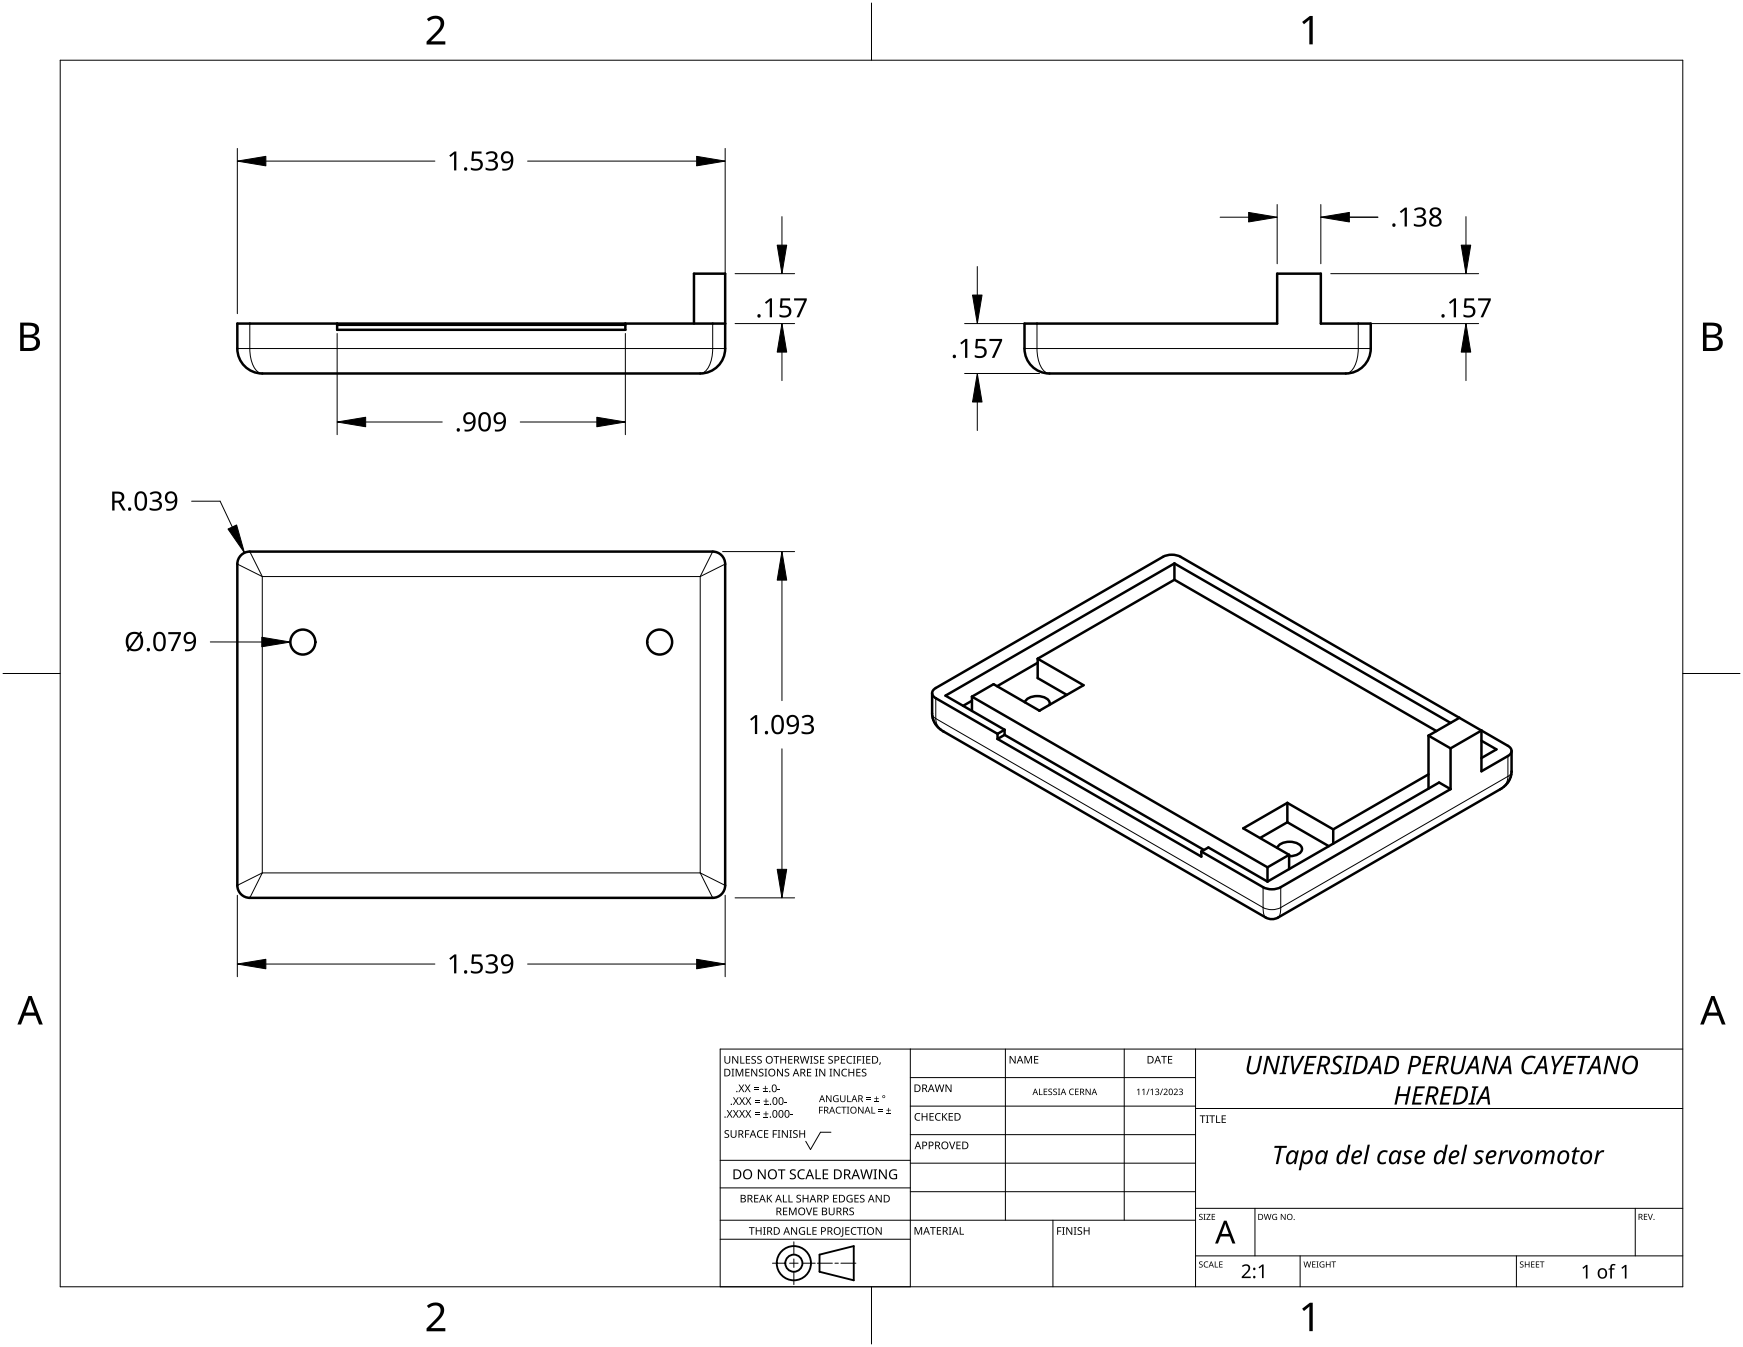
[picture p155: page 1]
