Adriana-28/Repositorio_grupo_13/Software/Codigo_Servo1_Servo2.ino

#include <Servo.h>
Servo servo1;
Servo servo2;

void setup() {
  servo1. attach(3);
  servo2.attach(5);
}

void loop() {
servo1.write(0);
servo2.write(0);
delay(2000);
servo1.write(180);
servo2.write(180);
delay(2000);
}
